hridaykrishna2007-a11y/Mini-Game-Console/ASSETS/CONSOLEFRONT.png

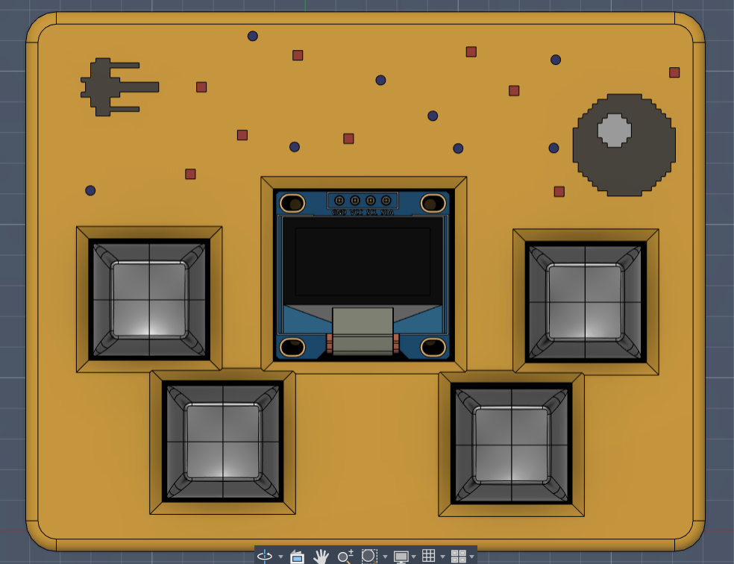
ASSETS/CONSOLEFRONT.png
