hridaykrishna2007-a11y/Mini-Game-Console/ASSETS/DEATHSTAR.png

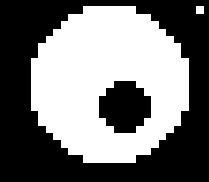
ASSETS/DEATHSTAR.png
