hridaykrishna2007-a11y/Mini-Game-Console/ASSETS/PCB(withoutpour).png

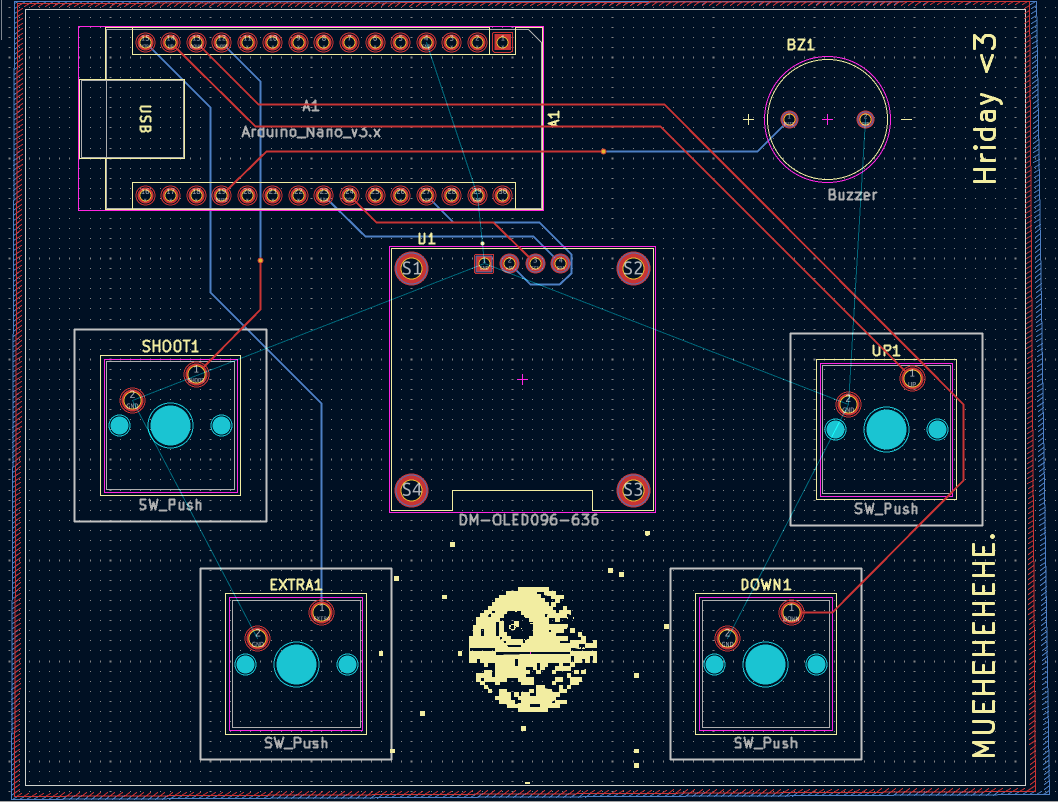
ASSETS/PCB(withoutpour).png
